Somni-Labs/somni-wearable-dock/docs/superpowers/plans/2026-05-22-esp32-rgb-logo.md

# ESP32 + RGB Underglow + Backlit Logo — Implementation Plan

> **For agentic workers:** REQUIRED SUB-SKILL: Use superpowers:subagent-driven-development (recommended) or superpowers:executing-plans to implement this plan task-by-task. Steps use checkbox (`- [ ]`) syntax for tracking.

**Goal:** Add an ESP32 mount, WS2812B RGB underglow channels, LED driver pocket, wiring grooves, and a backlit "Somni Labs" logo to the bottom tray.

**Architecture:** All changes are in `build_bottom_tray()` within `designs/v1-charging-stand.py`. New parametric constants are added to the constants section. The ESP32 mount and driver pocket are additive geometry (standoffs + cradle walls). Everything else is subtractive (channel cuts, slots, logo recess). No new files needed — just the design file and CLAUDE.md.

**Tech Stack:** CadQuery (Python)

---

## File Structure

| File | Responsibility | Change |
|---|---|---|
| `designs/v1-charging-stand.py` | Main parametric design | Add constants (lines ~132-155), add ESP32 mount + driver pocket + LED channels + light slots + wiring grooves + logo to `build_bottom_tray()` (before snap-fit clips section, ~line 487) |
| `CLAUDE.md` | Project documentation | Document ESP32/RGB/logo features |

---

### Task 1: Add parametric constants for ESP32, LED, logo, and driver

**Files:**
- Modify: `designs/v1-charging-stand.py` — constants section (after Mudra cable constants, ~line 132)

- [ ] **Step 1: Add all new constants**

After line 132 (`MUDRA_CABLE_BEND_R = 15`) and before `# --- Device 5: Even Realities G2 glasses case ---` (line 134), insert:

```python
# --- ESP32 DevKitC V4 mount ---
ESP32_L = 55 + 1          # board length + tolerance (along Y)
ESP32_W = 28 + 1          # board width + tolerance (along X)
ESP32_H = 12              # board height (tallest component)
ESP32_STANDOFF_H = 2      # standoff post height
ESP32_STANDOFF_D = 3      # standoff post diameter
ESP32_CRADLE_H = 6        # cradle wall height
ESP32_CRADLE_T = 1.5      # cradle wall thickness
ESP32_USB_SLOT_W = 12     # USB port slot width through front wall
ESP32_USB_SLOT_H = 8      # USB port slot height through front wall

# --- RGB LED strip (WS2812B 30/m) ---
LED_CHANNEL_W = 12        # channel width (10mm strip + clearance)
LED_CHANNEL_D = 4         # channel depth into floor
LED_SLOT_H = 3            # light exit slot height on exterior walls
LED_SLOT_Z = 1            # slot bottom edge Z (above desk)

# --- Backlit logo ---
LOGO_TEXT = "Somni Labs"
LOGO_FONT_SIZE = 12       # cap height in mm
LOGO_RECESS_DEPTH = 1.9   # cut depth (WALL - 0.6mm diffuser)
LOGO_Z = 20               # vertical center of text on front wall

# --- LED driver / level shifter mount ---
DRIVER_L = 22             # pocket length (Y)
DRIVER_W = 16             # pocket width (X)
DRIVER_H = 8              # pocket depth (Z)
DRIVER_STANDOFF_H = 2     # standoff height
DRIVER_STANDOFF_D = 2     # standoff diameter
```

- [ ] **Step 2: Verify syntax**

Run: `cd /home/curiosity/mounted_drives/obsidian/obsidian/Somni/SomniApps/somni-wearable-dock && python3 -c "exec(open('designs/v1-charging-stand.py').read().replace('from cq_server.ui import ui, show_object', '# removed').replace('show_object', '# show_object'))"`

Expected: No errors — constants are defined but not yet used.

- [ ] **Step 3: Commit**

```bash
git add designs/v1-charging-stand.py
git commit -m "feat: add parametric constants for ESP32, RGB LED, logo, and driver

Co-Authored-By: Claude Opus 4.6 <noreply@anthropic.com>"
```

---

### Task 2: Add ESP32 mount to `build_bottom_tray()`

**Files:**
- Modify: `designs/v1-charging-stand.py` — inside `build_bottom_tray()`, after the cable routing clips section (after line 481 `tray = tray.cut(arch_inner)`) and before `# ── Cable pass-through holes` (line 483)

- [ ] **Step 1: Add ESP32 mount geometry**

After the cable routing clips `for` loop (after the last `tray = tray.cut(arch_inner)`), add:

```python
    # ── ESP32 DevKitC V4 mount (front-left corner) ───────────────────────
    # Board oriented with long edge along Y (55mm), short edge (28mm, with
    # USB port) facing the front wall. Sits on standoff posts with cradle
    # walls on two sides for a snug drop-in fit.
    _esp_x = -STAND_W / 2 + WALL + ESP32_W / 2   # center X = -103mm
    _esp_y = -STAND_D / 2 + WALL + ESP32_L / 2   # center Y = -57mm

    # 4 standoff posts at mounting hole positions (2mm inset from board edges)
    _standoff_inset = 2
    for sx, sy in [
        (_esp_x - ESP32_W / 2 + _standoff_inset, _esp_y - ESP32_L / 2 + _standoff_inset),
        (_esp_x + ESP32_W / 2 - _standoff_inset, _esp_y - ESP32_L / 2 + _standoff_inset),
        (_esp_x - ESP32_W / 2 + _standoff_inset, _esp_y + ESP32_L / 2 - _standoff_inset),
        (_esp_x + ESP32_W / 2 - _standoff_inset, _esp_y + ESP32_L / 2 - _standoff_inset),
    ]:
        standoff = (
            cq.Workplane("XY")
            .workplane(offset=BASE_H)
            .center(sx, sy)
            .circle(ESP32_STANDOFF_D / 2)
            .extrude(ESP32_STANDOFF_H)
        )
        tray = tray.union(standoff)

    # Cradle wall — left side (against the left inner wall)
    cradle_left = (
        cq.Workplane("XY")
        .workplane(offset=BASE_H)
        .center(_esp_x - ESP32_W / 2 - ESP32_CRADLE_T / 2, _esp_y)
        .rect(ESP32_CRADLE_T, ESP32_L)
        .extrude(ESP32_CRADLE_H)
    )
    tray = tray.union(cradle_left)

    # Cradle wall — front side (against the front inner wall)
    cradle_front = (
        cq.Workplane("XY")
        .workplane(offset=BASE_H)
        .center(_esp_x, _esp_y - ESP32_L / 2 - ESP32_CRADLE_T / 2)
        .rect(ESP32_W, ESP32_CRADLE_T)
        .extrude(ESP32_CRADLE_H)
    )
    tray = tray.union(cradle_front)

    # USB port slot through the front wall
    _usb_z = BASE_H + ESP32_STANDOFF_H + 4   # center of USB port
    esp_usb_slot = (
        cq.Workplane("XY")
        .workplane(offset=_usb_z - ESP32_USB_SLOT_H / 2)
        .center(_esp_x, -STAND_D / 2)
        .rect(ESP32_USB_SLOT_W, WALL * 3)
        .extrude(ESP32_USB_SLOT_H)
    )
    tray = tray.cut(esp_usb_slot)
```

- [ ] **Step 2: Verify build succeeds**

Run: `cd /home/curiosity/mounted_drives/obsidian/obsidian/Somni/SomniApps/somni-wearable-dock && python3 export_charging_stand.py`

Expected: Build succeeds, 4 STL files exported. Bottom tray now has standoff posts, cradle walls, and USB slot.

- [ ] **Step 3: Commit**

```bash
git add designs/v1-charging-stand.py
git commit -m "feat: add ESP32 DevKitC V4 mount in bottom tray front-left corner

4 standoff posts, 2 cradle walls, USB port slot through front wall.

Co-Authored-By: Claude Opus 4.6 <noreply@anthropic.com>"
```

---

### Task 3: Add LED driver pocket to `build_bottom_tray()`

**Files:**
- Modify: `designs/v1-charging-stand.py` — inside `build_bottom_tray()`, directly after the ESP32 mount code added in Task 2

- [ ] **Step 1: Add driver pocket geometry**

After the ESP32 USB slot cut (`tray = tray.cut(esp_usb_slot)`), add:

```python
    # ── LED driver / level shifter pocket ────────────────────────────────
    # Small component pocket behind the ESP32 for the 3.3V→5V level shifter.
    # Sits between the ESP32 and the left wall LED channel start.
    _drv_x = _esp_x                                      # aligned with ESP32 center X
    _drv_y = _esp_y + ESP32_L / 2 + 5 + DRIVER_L / 2    # 5mm gap behind ESP32

    # Pocket cut into the floor
    driver_pocket = (
        cq.Workplane("XY")
        .workplane(offset=BASE_H - 0.5)
        .center(_drv_x, _drv_y)
        .rect(DRIVER_W, DRIVER_L)
        .extrude(DRIVER_H + 0.5)
    )
    tray = tray.cut(driver_pocket)

    # 2 standoff posts inside the pocket
    for dy_sign in [-1, 1]:
        drv_standoff = (
            cq.Workplane("XY")
            .workplane(offset=BASE_H)
            .center(_drv_x, _drv_y + dy_sign * (DRIVER_L / 2 - 3))
            .circle(DRIVER_STANDOFF_D / 2)
            .extrude(DRIVER_STANDOFF_H)
        )
        tray = tray.union(drv_standoff)
```

- [ ] **Step 2: Verify build succeeds**

Run: `cd /home/curiosity/mounted_drives/obsidian/obsidian/Somni/SomniApps/somni-wearable-dock && python3 export_charging_stand.py`

Expected: Build succeeds. Bottom tray now has driver pocket behind ESP32.

- [ ] **Step 3: Commit**

```bash
git add designs/v1-charging-stand.py
git commit -m "feat: add LED driver/level shifter pocket behind ESP32

22x16x8mm pocket with 2 standoff posts for level shifter board.

Co-Authored-By: Claude Opus 4.6 <noreply@anthropic.com>"
```

---

### Task 4: Add RGB LED channel and light exit slots to `build_bottom_tray()`

**Files:**
- Modify: `designs/v1-charging-stand.py` — inside `build_bottom_tray()`, directly after the driver pocket code added in Task 3

- [ ] **Step 1: Add U-shaped LED channel and light exit slots**

After the driver standoff code (`tray = tray.union(drv_standoff)`), add:

```python
    # ── RGB LED channel (U-shaped: left wall → front wall → right wall) ──
    # Groove in the floor for WS2812B LED strip. Inset 1mm from the inner
    # wall so light reflects off the wall before exiting through the slots.
    _inner_left   = -STAND_W / 2 + WALL            # X = -117.5
    _inner_right  =  STAND_W / 2 - WALL            # X =  117.5
    _inner_front  = -STAND_D / 2 + WALL             # Y = -85
    _inner_back   =  STAND_D / 2 - WALL             # Y =  85
    _ch_inset = 1   # inset from inner wall face
    _ch_z = BASE_H - LED_CHANNEL_D  # channel bottom (may cut into floor)

    # Left wall segment (runs along Y)
    led_ch_left = (
        cq.Workplane("XY")
        .workplane(offset=_ch_z)
        .center(_inner_left + _ch_inset + LED_CHANNEL_W / 2,
                (_inner_front + _inner_back) / 2)
        .rect(LED_CHANNEL_W, _inner_back - _inner_front)
        .extrude(LED_CHANNEL_D + 0.5)
    )
    tray = tray.cut(led_ch_left)

    # Front wall segment (runs along X)
    led_ch_front = (
        cq.Workplane("XY")
        .workplane(offset=_ch_z)
        .center(0, _inner_front + _ch_inset + LED_CHANNEL_W / 2)
        .rect(_inner_right - _inner_left, LED_CHANNEL_W)
        .extrude(LED_CHANNEL_D + 0.5)
    )
    tray = tray.cut(led_ch_front)

    # Right wall segment (runs along Y)
    led_ch_right = (
        cq.Workplane("XY")
        .workplane(offset=_ch_z)
        .center(_inner_right - _ch_inset - LED_CHANNEL_W / 2,
                (_inner_front + _inner_back) / 2)
        .rect(LED_CHANNEL_W, _inner_back - _inner_front)
        .extrude(LED_CHANNEL_D + 0.5)
    )
    tray = tray.cut(led_ch_right)

    # ── Light exit slots (exterior walls, near desk level) ───────────────
    # Narrow horizontal slots cut through the bottom of each exterior wall.
    # Light from the LED channel spills downward onto the desk.

    # Front wall light slot
    led_slot_front = (
        cq.Workplane("XY")
        .workplane(offset=LED_SLOT_Z)
        .center(0, -STAND_D / 2)
        .rect(STAND_W - CORNER_R * 4, WALL * 3)
        .extrude(LED_SLOT_H)
    )
    tray = tray.cut(led_slot_front)

    # Left wall light slot
    led_slot_left = (
        cq.Workplane("XY")
        .workplane(offset=LED_SLOT_Z)
        .center(-STAND_W / 2, 0)
        .rect(WALL * 3, STAND_D - CORNER_R * 4)
        .extrude(LED_SLOT_H)
    )
    tray = tray.cut(led_slot_left)

    # Right wall light slot
    led_slot_right = (
        cq.Workplane("XY")
        .workplane(offset=LED_SLOT_Z)
        .center(STAND_W / 2, 0)
        .rect(WALL * 3, STAND_D - CORNER_R * 4)
        .extrude(LED_SLOT_H)
    )
    tray = tray.cut(led_slot_right)
```

- [ ] **Step 2: Verify build succeeds**

Run: `cd /home/curiosity/mounted_drives/obsidian/obsidian/Somni/SomniApps/somni-wearable-dock && python3 export_charging_stand.py`

Expected: Build succeeds. Bottom tray now has LED channels in the floor and light exit slots on three walls.

- [ ] **Step 3: Commit**

```bash
git add designs/v1-charging-stand.py
git commit -m "feat: add U-shaped RGB LED channel and light exit slots

12mm wide floor channel on three sides (left, front, right) with 3mm
light exit slots at the base of exterior walls for desk underglow.

Co-Authored-By: Claude Opus 4.6 <noreply@anthropic.com>"
```

---

### Task 5: Add wiring grooves to `build_bottom_tray()`

**Files:**
- Modify: `designs/v1-charging-stand.py` — inside `build_bottom_tray()`, directly after the LED channel code added in Task 4

- [ ] **Step 1: Add floor wiring grooves**

After the right wall light slot cut (`tray = tray.cut(led_slot_right)`), add:

```python
    # ── Floor wiring grooves ─────────────────────────────────────────────
    # Shallow channels in the floor for routing wires between the ESP32,
    # driver pocket, LED channel, and charger bay.
    _wire_w = 6    # groove width
    _wire_d = 3    # groove depth
    _wire_z = BASE_H - _wire_d

    # Groove 1: ESP32 → driver pocket (short Y-axis run)
    wire_esp_to_drv = (
        cq.Workplane("XY")
        .workplane(offset=_wire_z)
        .center(_esp_x, (_esp_y + _drv_y) / 2)
        .rect(_wire_w, abs(_drv_y - _esp_y) + ESP32_L / 2 + DRIVER_L / 2)
        .extrude(_wire_d + 0.5)
    )
    tray = tray.cut(wire_esp_to_drv)

    # Groove 2: Driver pocket → left wall LED channel start (short X-axis run)
    _led_ch_x = _inner_left + _ch_inset + LED_CHANNEL_W / 2
    wire_drv_to_led = (
        cq.Workplane("XY")
        .workplane(offset=_wire_z)
        .center((_drv_x + _led_ch_x) / 2, _drv_y)
        .rect(abs(_drv_x - _led_ch_x) + DRIVER_W / 2 + LED_CHANNEL_W / 2, _wire_w)
        .extrude(_wire_d + 0.5)
    )
    tray = tray.cut(wire_drv_to_led)

    # Groove 3: ESP32 → charger bay (USB power cable from VanBon)
    # Runs from ESP32 position rightward (+X) to the charger bay left edge
    wire_esp_to_charger = (
        cq.Workplane("XY")
        .workplane(offset=_wire_z)
        .center((_esp_x + _charger_left) / 2, _esp_y)
        .rect(abs(_charger_left - _esp_x) + ESP32_W / 2, _wire_w)
        .extrude(_wire_d + 0.5)
    )
    tray = tray.cut(wire_esp_to_charger)
```

- [ ] **Step 2: Verify build succeeds**

Run: `cd /home/curiosity/mounted_drives/obsidian/obsidian/Somni/SomniApps/somni-wearable-dock && python3 export_charging_stand.py`

Expected: Build succeeds. Floor now has wiring grooves connecting ESP32 → driver → LED channel and ESP32 → charger bay.

- [ ] **Step 3: Commit**

```bash
git add designs/v1-charging-stand.py
git commit -m "feat: add floor wiring grooves for ESP32/driver/LED/charger

Three shallow 6mm channels connecting ESP32 to driver pocket, driver
to LED channel start, and ESP32 to charger bay for USB power cable.

Co-Authored-By: Claude Opus 4.6 <noreply@anthropic.com>"
```

---

### Task 6: Add "Somni Labs" backlit logo to `build_bottom_tray()`

**Files:**
- Modify: `designs/v1-charging-stand.py` — inside `build_bottom_tray()`, directly after the wiring grooves code added in Task 5

This task uses CadQuery's `text()` method to create recessed text on the front wall exterior.

- [ ] **Step 1: Add logo recess**

After the charger wire groove cut (`tray = tray.cut(wire_esp_to_charger)`), add:

```python
    # ── "Somni Labs" backlit logo (front wall exterior) ──────────────────
    # Text recessed into the front wall, leaving a 0.6mm thin wall as a
    # natural light diffuser. The RGB strip behind the front wall
    # backlights the letters for a soft glow effect.
    _logo_y = -STAND_D / 2  # exterior face of front wall
    logo_text = (
        cq.Workplane("XZ")
        .workplane(offset=-_logo_y)  # position at front wall exterior face
        .center(0, LOGO_Z)
        .text(LOGO_TEXT, LOGO_FONT_SIZE, -LOGO_RECESS_DEPTH,
              font="Sans", halign="center", valign="center")
    )
    tray = tray.cut(logo_text)
```

**Note on `cq.Workplane.text()` parameters:**
- First arg: text string
- Second arg: font size (cap height in mm)
- Third arg: extrude depth — negative value cuts inward from the workplane face
- `font="Sans"` uses the system sans-serif font (available in the CadQuery container)
- `halign`/`valign` center the text at the workplane origin

- [ ] **Step 2: Verify build succeeds**

Run: `cd /home/curiosity/mounted_drives/obsidian/obsidian/Somni/SomniApps/somni-wearable-dock && python3 export_charging_stand.py`

Expected: Build succeeds. The bottom tray front wall now has "Somni Labs" recessed into the exterior face.

- [ ] **Step 3: Commit**

```bash
git add designs/v1-charging-stand.py
git commit -m "feat: add backlit Somni Labs logo on front wall

Text recessed 1.9mm into the 2.5mm front wall, leaving a 0.6mm
thin-wall diffuser. RGB strip behind the wall backlights the letters.

Co-Authored-By: Claude Opus 4.6 <noreply@anthropic.com>"
```

---

### Task 7: Update CLAUDE.md and verify full build

**Files:**
- Modify: `CLAUDE.md`

- [ ] **Step 1: Add ESP32/RGB/logo documentation to CLAUDE.md**

In the Architecture section, after the line about `scripts/pre-print-check.sh`, add:

```markdown
- **ESP32 mount** — DevKitC V4 cradle in bottom tray front-left corner, USB port through front wall
- **RGB underglow** — WS2812B LED strip channel (U-shaped: left, front, right walls) with 3mm light exit slots at base
- **Backlit logo** — "Somni Labs" recessed into front wall exterior with 0.6mm thin-wall diffuser, backlit by RGB strip
- **LED driver pocket** — Level shifter mount behind ESP32 for 3.3V→5V logic conversion
```

- [ ] **Step 2: Run full export to verify all parts build**

Run: `cd /home/curiosity/mounted_drives/obsidian/obsidian/Somni/SomniApps/somni-wearable-dock && python3 export_charging_stand.py`

Expected: All 4 STL files and 4 STEP files exported successfully.

- [ ] **Step 3: Verify output files**

Run: `ls -lh output/*.stl`

Expected: 4 STL files. Bottom tray size may have changed slightly due to new geometry.

- [ ] **Step 4: Commit**

```bash
git add CLAUDE.md
git commit -m "docs: document ESP32, RGB underglow, backlit logo, and driver mount

Co-Authored-By: Claude Opus 4.6 <noreply@anthropic.com>"
```

---

### Task 8: Push, re-export, and render in cadquery-server

**Files:**
- No code changes — verification and deployment

- [ ] **Step 1: Push to GitHub**

Run: `git push origin main`

- [ ] **Step 2: Restart cadquery-server**

Run: `kubectl rollout restart deployment cadquery-server -n utilities`

- [ ] **Step 3: Verify cadquery-server renders the updated bottom tray**

Wait for rollout to complete, then verify the server returns geometry:

Run: `kubectl rollout status deployment cadquery-server -n utilities --timeout=60s`

Then check the preview API responds with all 4 parts:

Run: `curl -s --max-time 60 "http://10.43.126.202:5000/json?m=v1-charging-stand" | python3 -c "import json,sys; data=json.load(sys.stdin); names=[p['name'] for p in data['model'][0]['parts']]; print(f'Parts: {names}')"`

Expected: `Parts: ['bottom_tray', 'top_tray', 'ipad_cover', 'mudra_pole']`

Check the browser preview at `cadquery-somni-labs.tail58c8e4.ts.net` to visually confirm:
- ESP32 cradle mount visible in front-left corner
- Driver pocket visible behind ESP32
- LED channel grooves along three walls
- Light exit slots at the base of exterior walls
- "Somni Labs" text recessed into front wall
- Wiring grooves connecting components
