Somni-Labs/somni-wearable-dock/output/v1-charging-stand-tilt-plate-uh.step

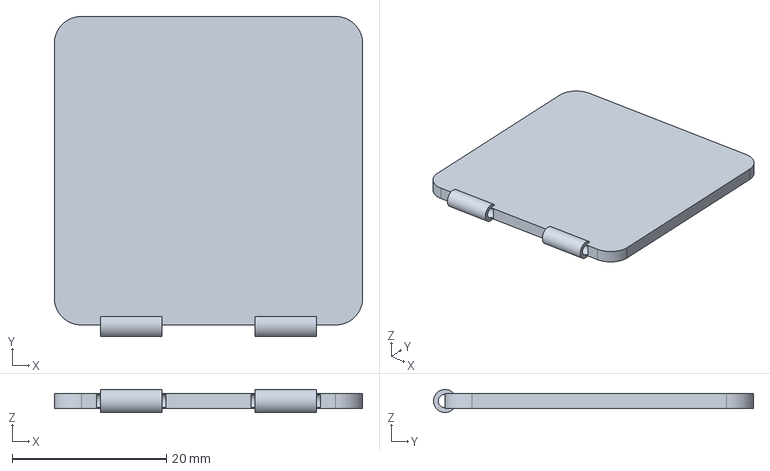
[picture p15: CAD file, 2026-06-08]
output/v1-charging-stand-tilt-plate-uh.step
40.0 x 41.5 x 3.00 mm
